Sarbf1/Gas-sens_Rs-485/Simulations/Sensor_Signal.asc

C1: cap; 1µ
C2: cap; 1µ
I1: current; 40µ
R1: res; 10k
R2: res; 10
R3: res; 1k
R4: res; 1k
R5: res; 10K
R6: res; 10
R7: res; 100k
R8: res; 100k
U1: MAX4230
U2: MAX4230
V1: voltage; 3.3
Named nets: 0, Sensor_U_Out, Reference, Working, Counter
.dc I1 0 40u
