Sarbf1/Gas-sens_Rs-485/Simulations/PWM-to-AnalogOutput.asc

C1: cap; 470n
R1: res; 1k
R2: res; 2.2k
R3: res; 1k
R4: res; 470
R5: res; 10k
U1: MAX44248
V1: voltage; PULSE(0 3.3 8u 0 0 8u 16u 1000)
V2: voltage; 24
Named nets: 0, U_Out, I_Out, PWM, DC_Signal
.tran 0 5m 0 0.0002m
