Sarbf1/Gas-sens_Rs-485/Software_Breadboard/Breadboard_developement/Core/Inc/mmodbusConfig.h

#ifndef _MMODBUS_CONFIG_H_
#define _MMODBUS_CONFIG_H_

#define _MMODBUS_FREERTOS         0
#define _MMODBUS_RTU              0
#define _MMODBUS_ASCII            0 //  not implemented yet
#define _MMODBUS_USART            USART1             
#define _MMODBUS_RXSIZE           64  
#define _MMODBUS_TXDMA            0
#if     _MMODBUS_TXDMA == 1
#define _MMODBUS_DMA              DMA2
#define _MMODBUS_DMASTREAM        LL_DMA_STREAM_7   
#endif
#define _MMODBUS_CTRL_GPIO      GPIOA			//RS485_CTRL_GPIO_Port
#define _MMODBUS_CTRL_PIN       GPIO_PIN_12  	//RS485_CTRL_Pin


#if (_MMODBUS_RTU == 1) && (_MMODBUS_ASCII == 1)
#error please select _MMODBUS_RTU or _MMODBUS_ASCII
#endif
#endif
