Sarbf1/Gas-sens_Rs-485/Software_Breadboard/Board_Dev-layout/Core/Inc/modbus_crc.h

/*
 * modbus_crc.h
 *
 *  Created on: Sep 16, 2022
 *      Author: arunr
 */

#ifndef INC_MODBUS_CRC_H_
#define INC_MODBUS_CRC_H_
#include "stdint.h"

uint16_t crc16(uint8_t *buffer, uint16_t buffer_length);


#endif /* INC_MODBUS_CRC_H_ */
